ka6s/rp_adapter/BlockDiag.jpg

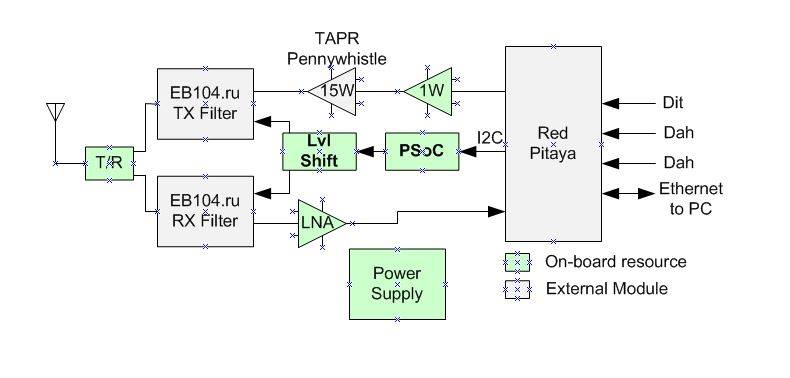
BlockDiag.jpg
