ka6s/rp_adapter/knobs_back.jpg

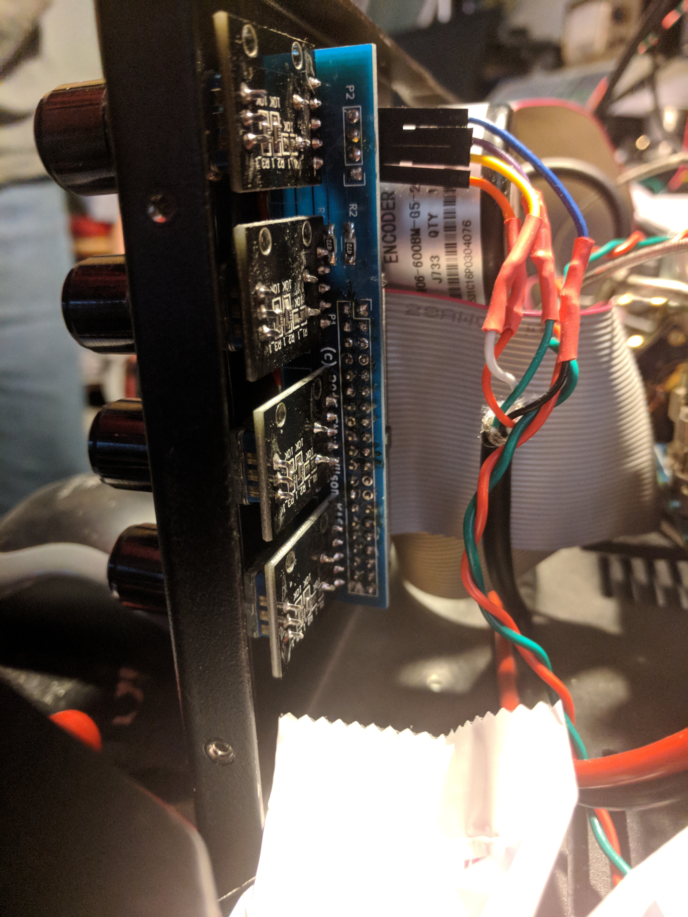
knobs_back.jpg
