ka6s/rp_adapter/messysystem.jpg

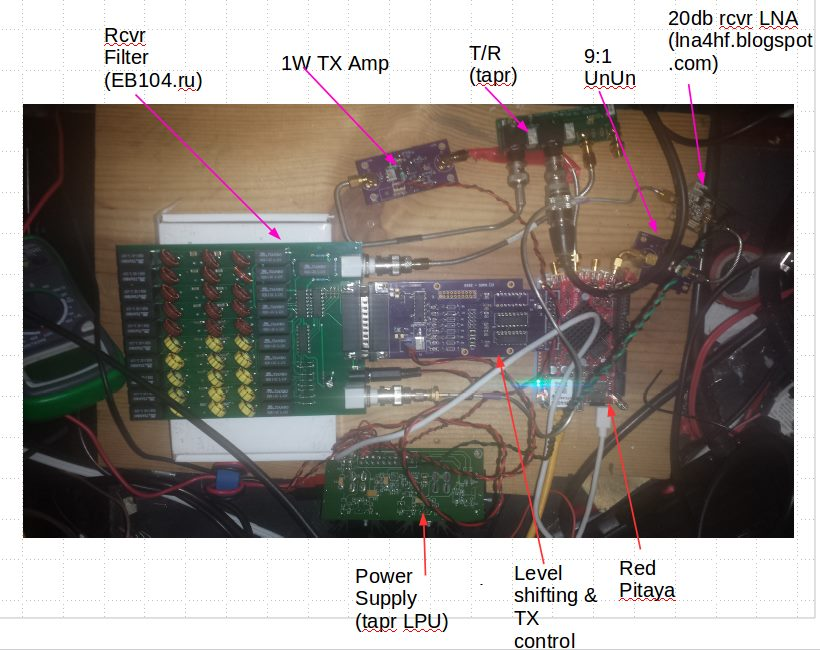
messysystem.jpg
