ka6s/rp_adapter/MezaninePower.jpeg

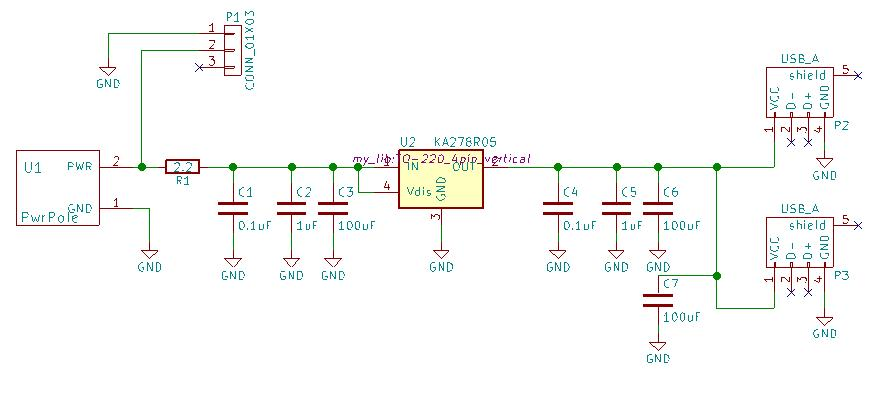
MezaninePower.jpeg
