ka6s/rp_adapter/OneWattPa.jpeg

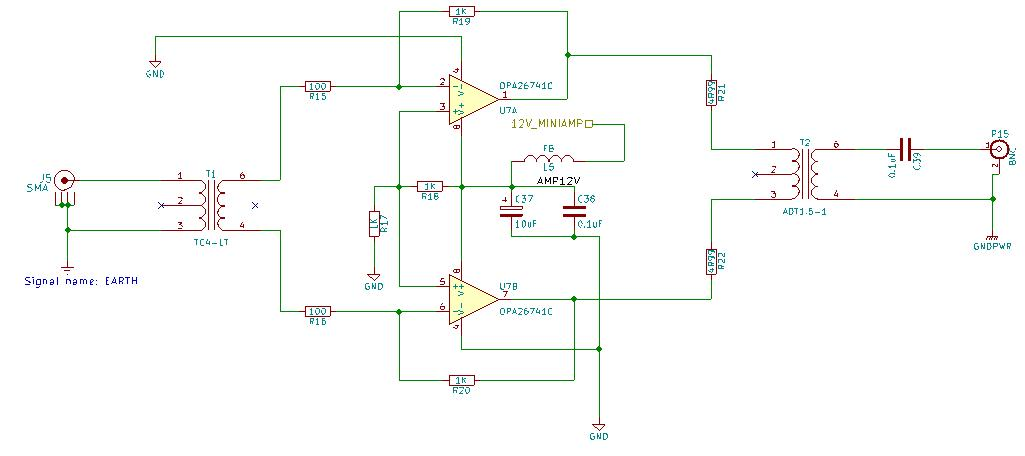
OneWattPa.jpeg
