ka6s/rp_adapter/PA.jpg

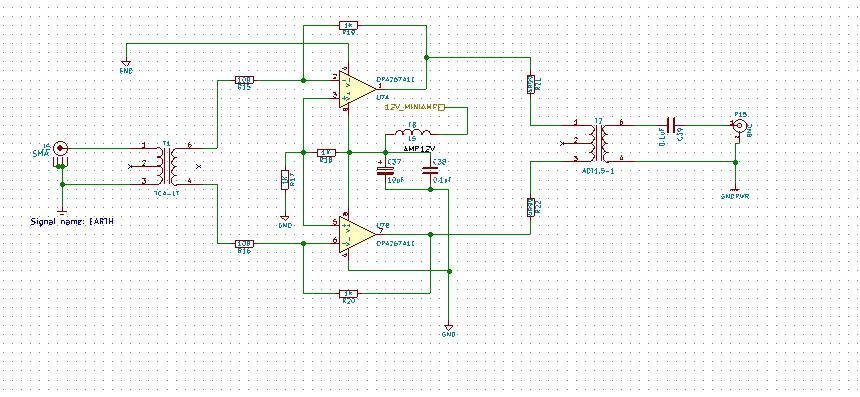
PA.jpg
