ka6s/rp_adapter/PiHPSDR_image2.jpg

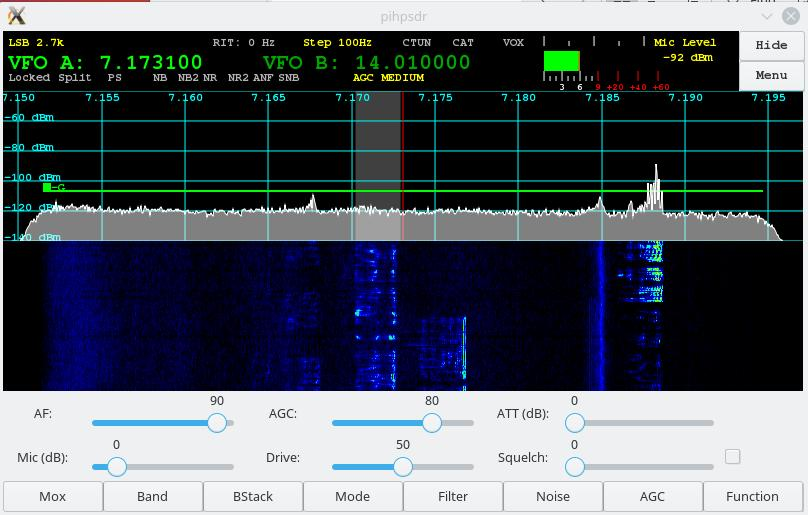
PiHPSDR_image2.jpg
