ka6s/rp_adapter/PiHPSDR_image.jpeg

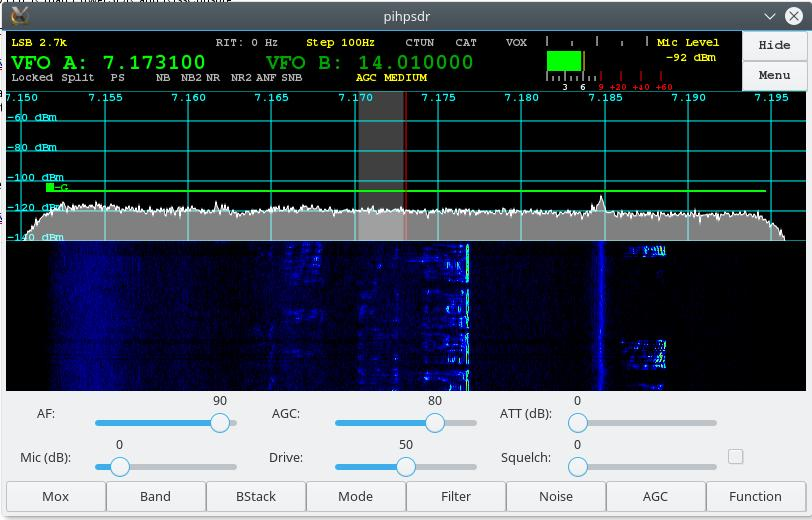
PiHPSDR_image.jpeg
