ka6s/rp_adapter/PiHPSSDR_image3.jpeg

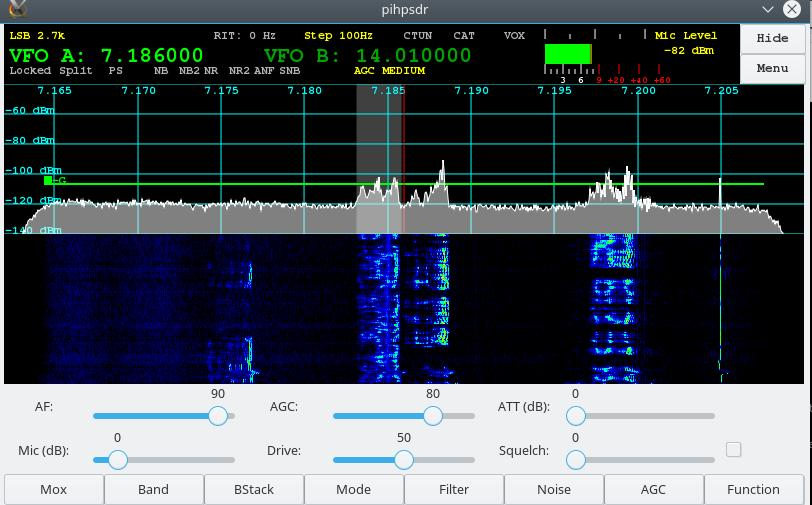
PiHPSSDR_image3.jpeg
