ka6s/rp_adapter/Power_AddOn.jpg

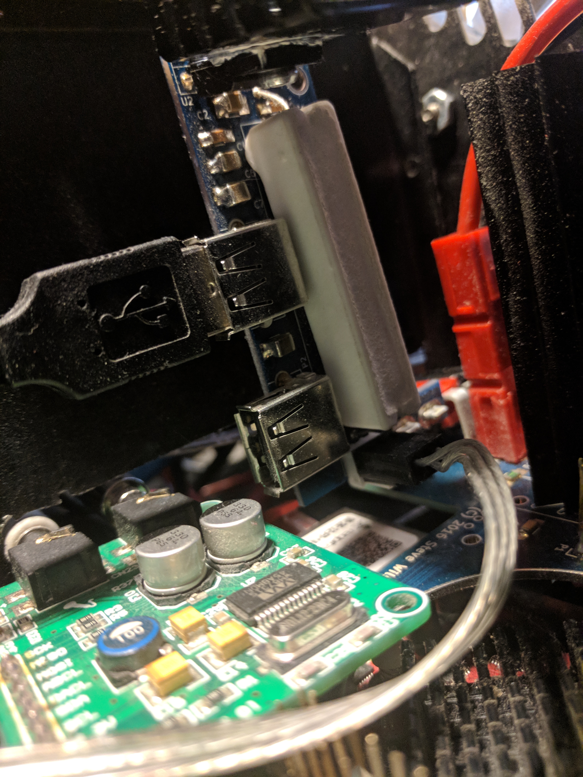
Power_AddOn.jpg
