ka6s/rp_adapter/redp.jpg

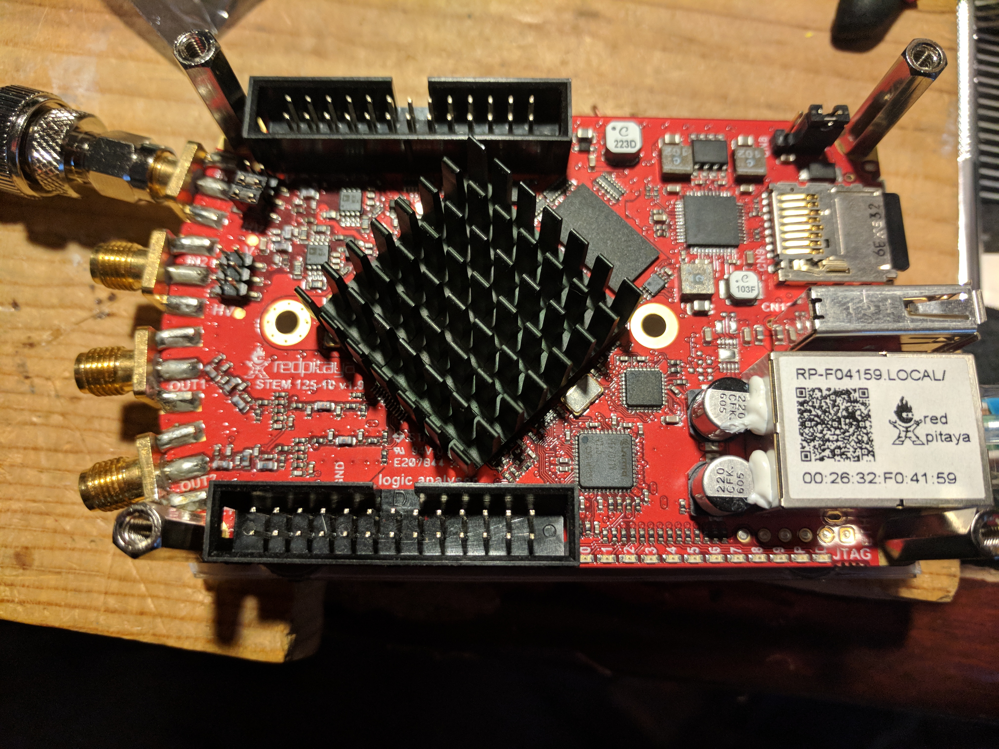
redp.jpg
