ka6s/rp_adapter/rev2.jpg

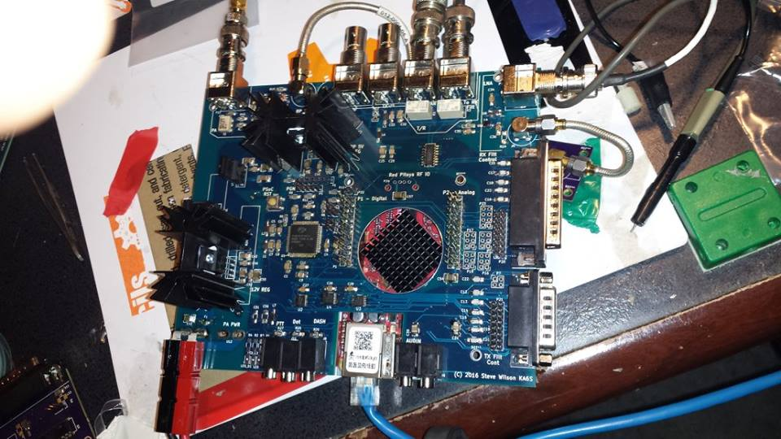
rev2.jpg
