ka6s/rp_adapter/Rev3.jpg

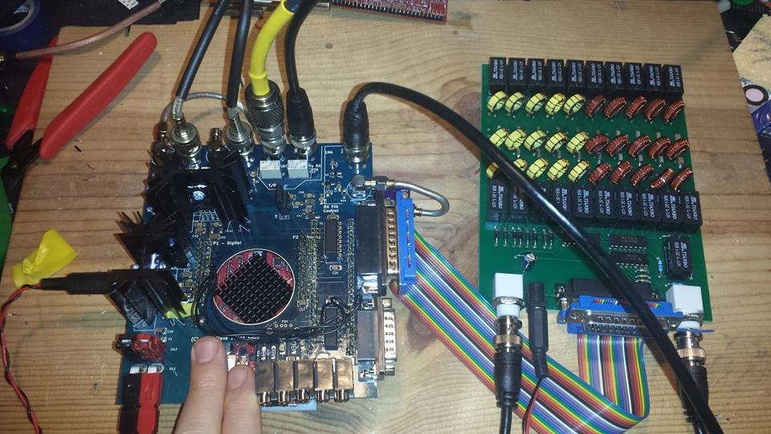
Rev3.jpg
