ka6s/rp_adapter/rev3_with_raspberrypi.jpg

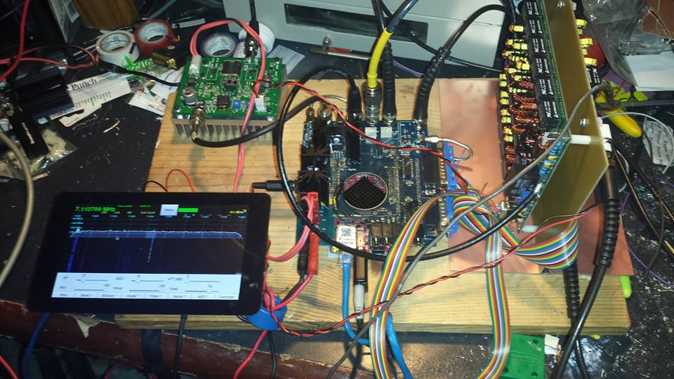
rev3_with_raspberrypi.jpg
