ka6s/rp_adapter/rotary_encoder_schem.jpeg

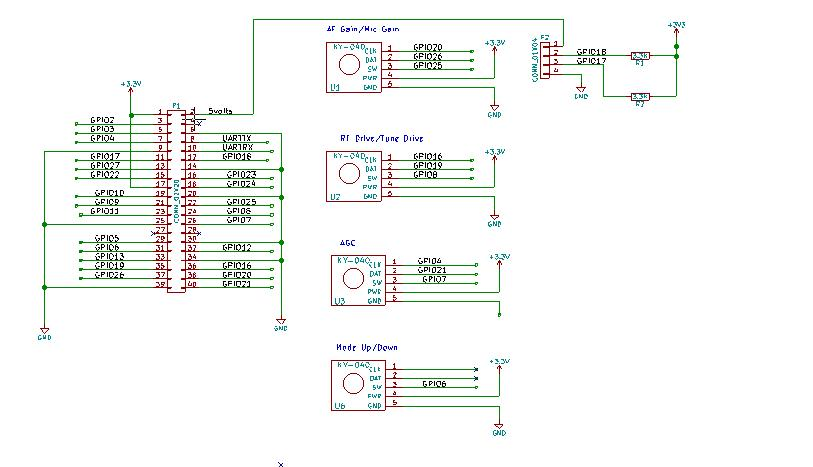
rotary_encoder_schem.jpeg
