ka6s/rp_adapter/rp2rev1.jpg

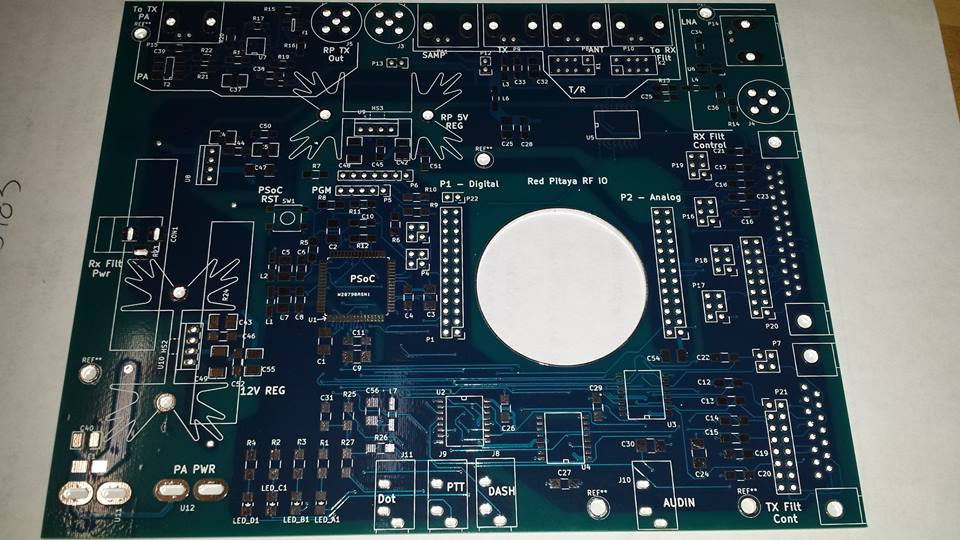
rp2rev1.jpg
