ka6s/rp_adapter/rp3_ver3_versus_ver2.jpg

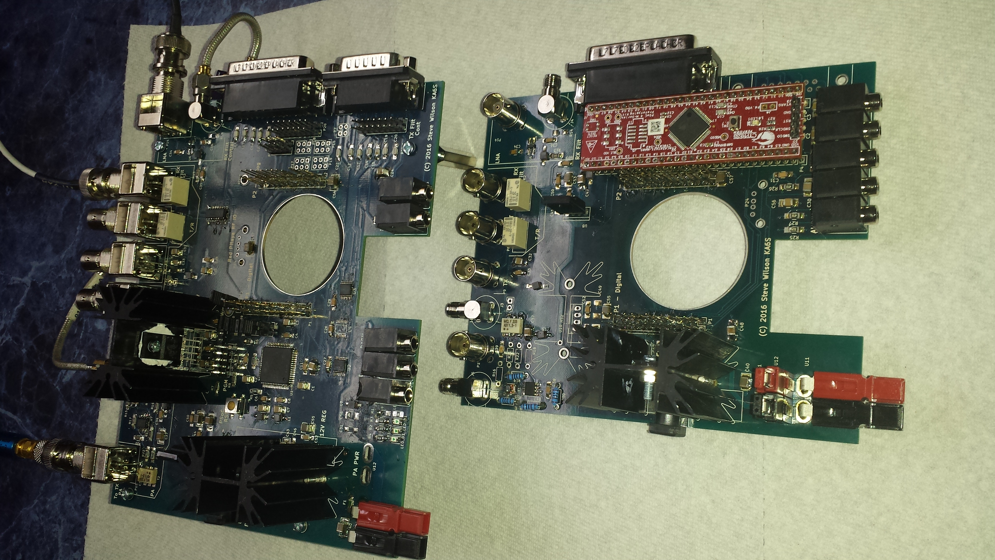
rp3_ver3_versus_ver2.jpg
