ka6s/rp_adapter/unun.jpg

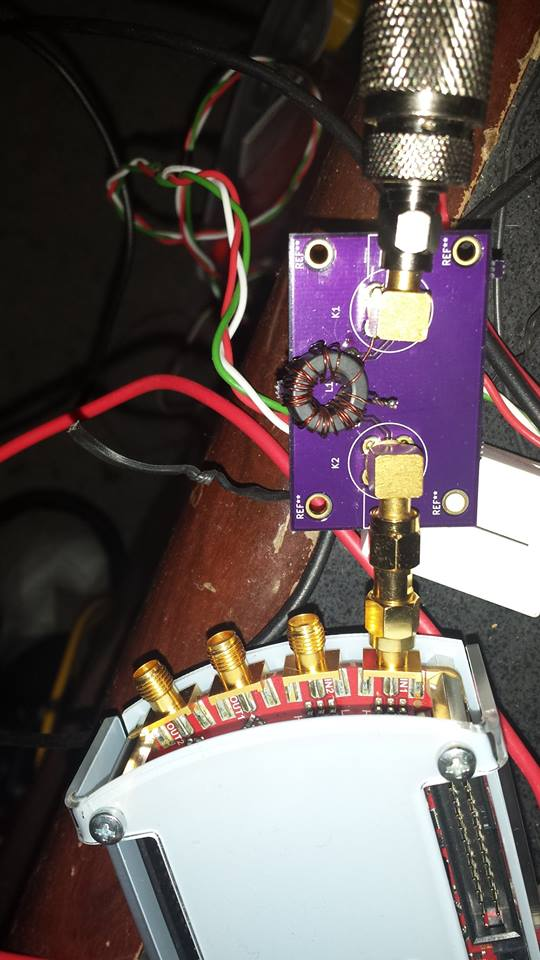
unun.jpg
