ka6s/rp_adapter/docs/rp_adapter.pdf

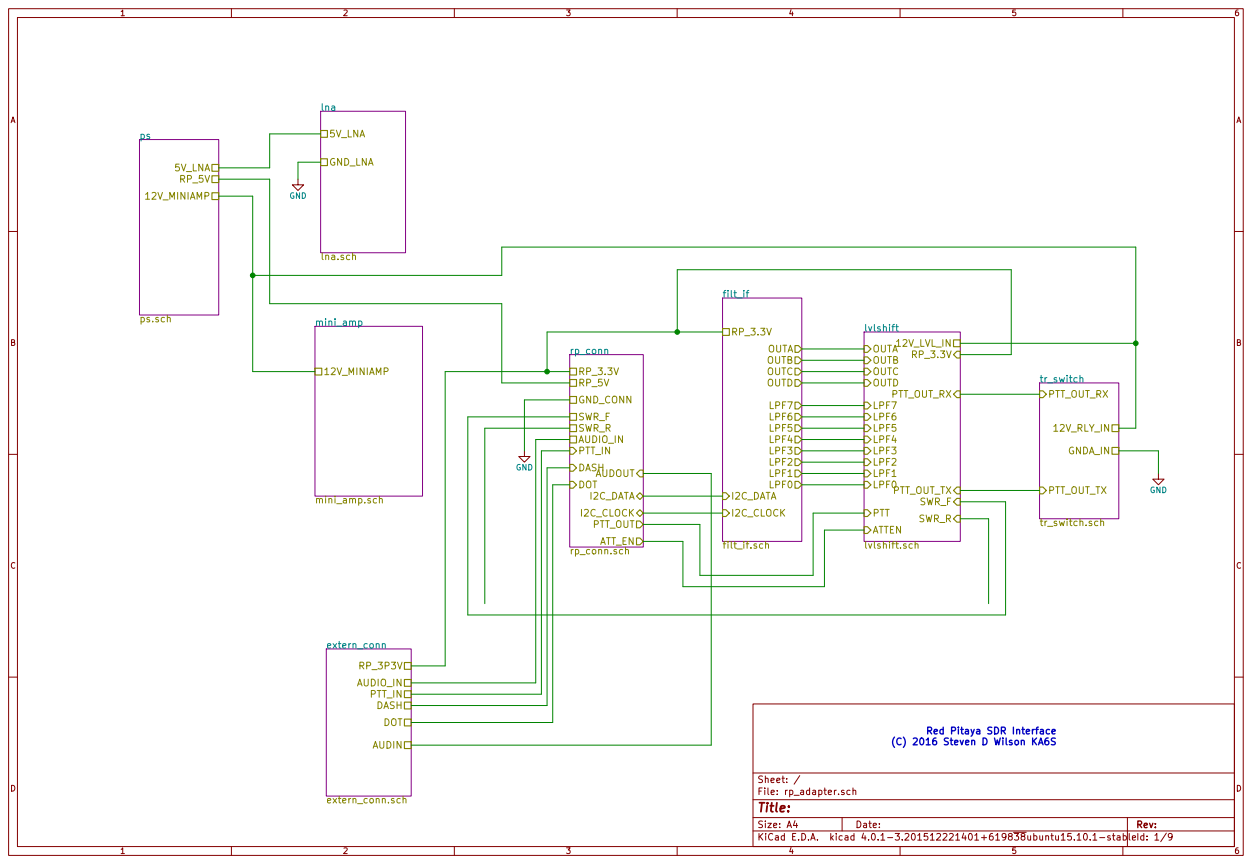
[picture p25: page 1]

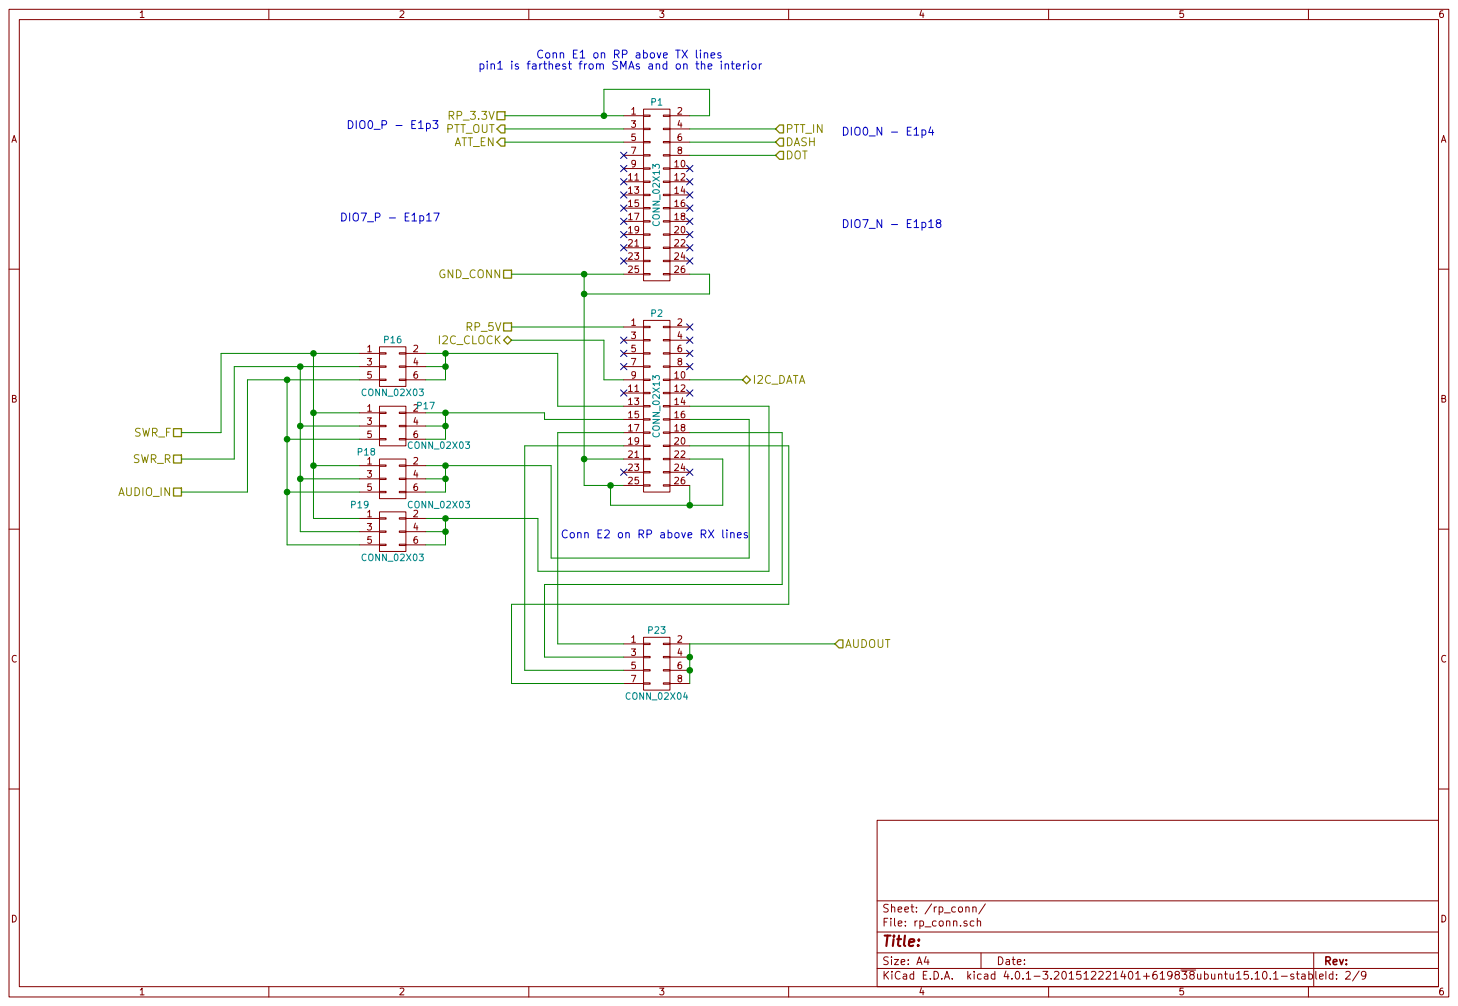
[picture p26: page 2]

pin1 is farthest from SMAs and on the interior

5 3 | 6P17 CONN_02X03 4

15 | 16
17 | 18

Conn E2 on RP above RX lines

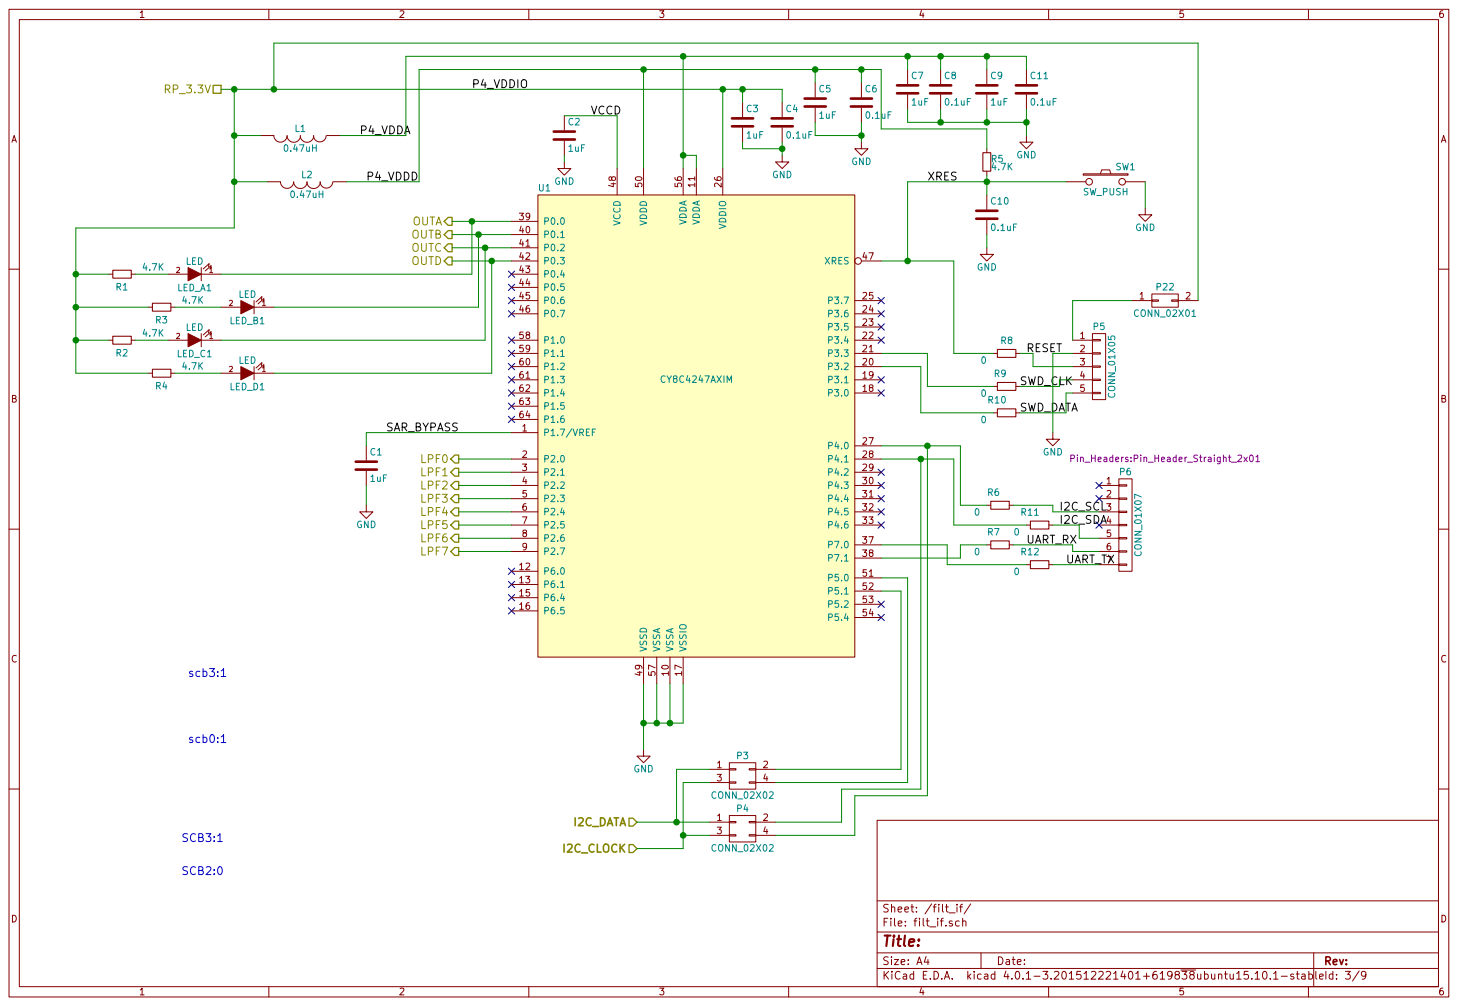
[picture p27: page 3]

VCCD | C3

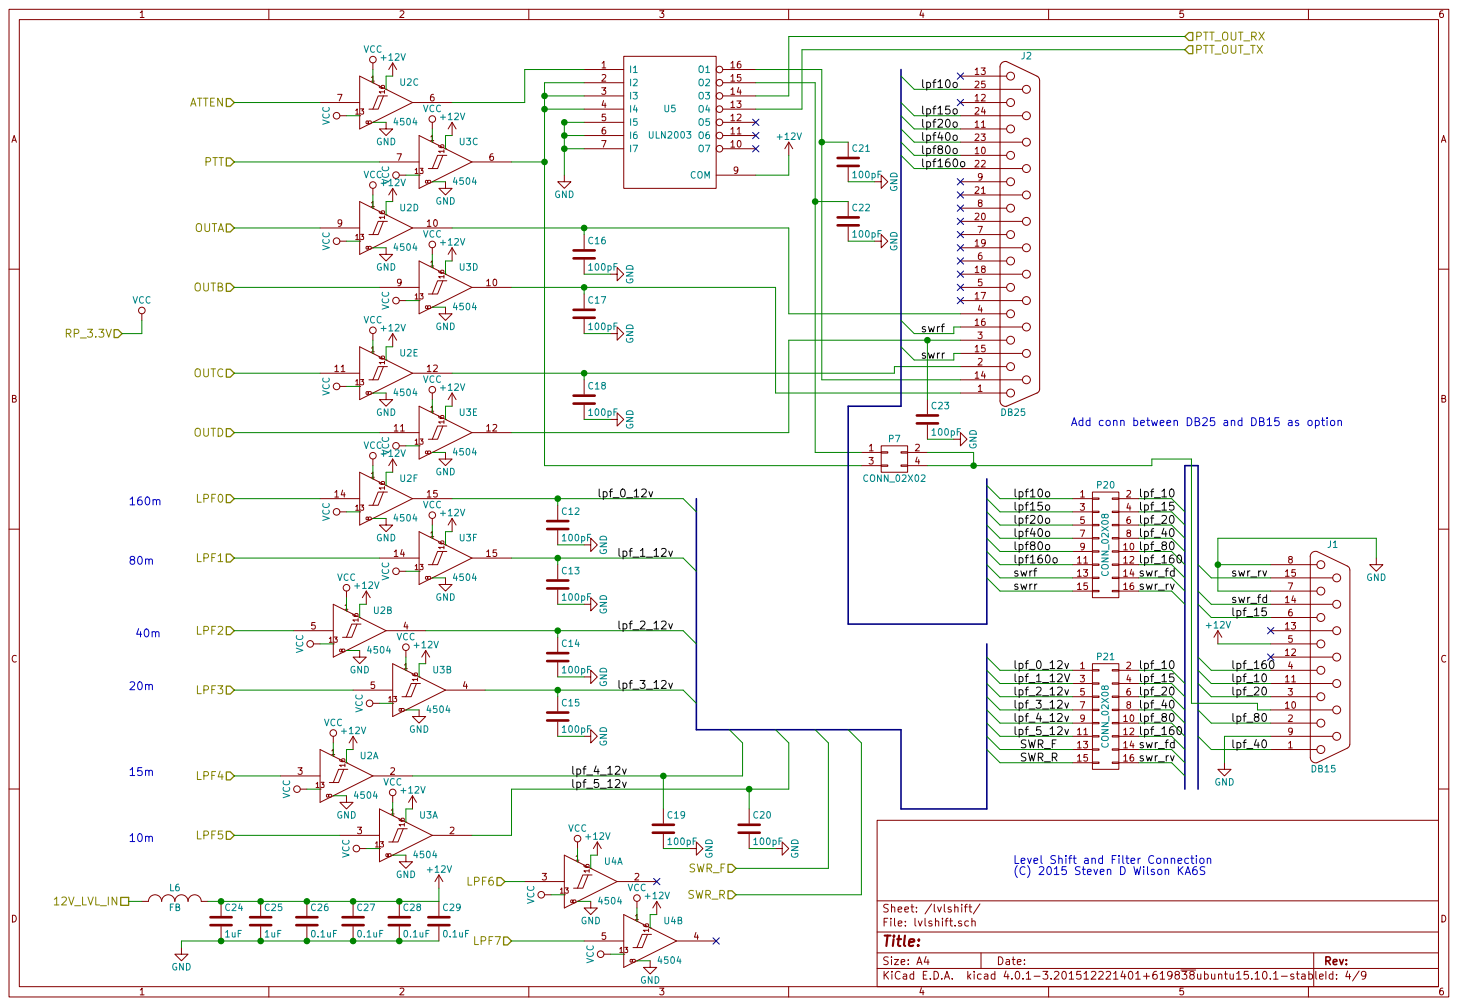
[picture p28: page 4]

14

Add conn between DB25 and DB15 as option

Level Shift and Filter Connection
(C) 2015 Steven D Wilson KA6S

Id: 4/9 Title: File: lvlshift.sch Sheet: /lvlshift/

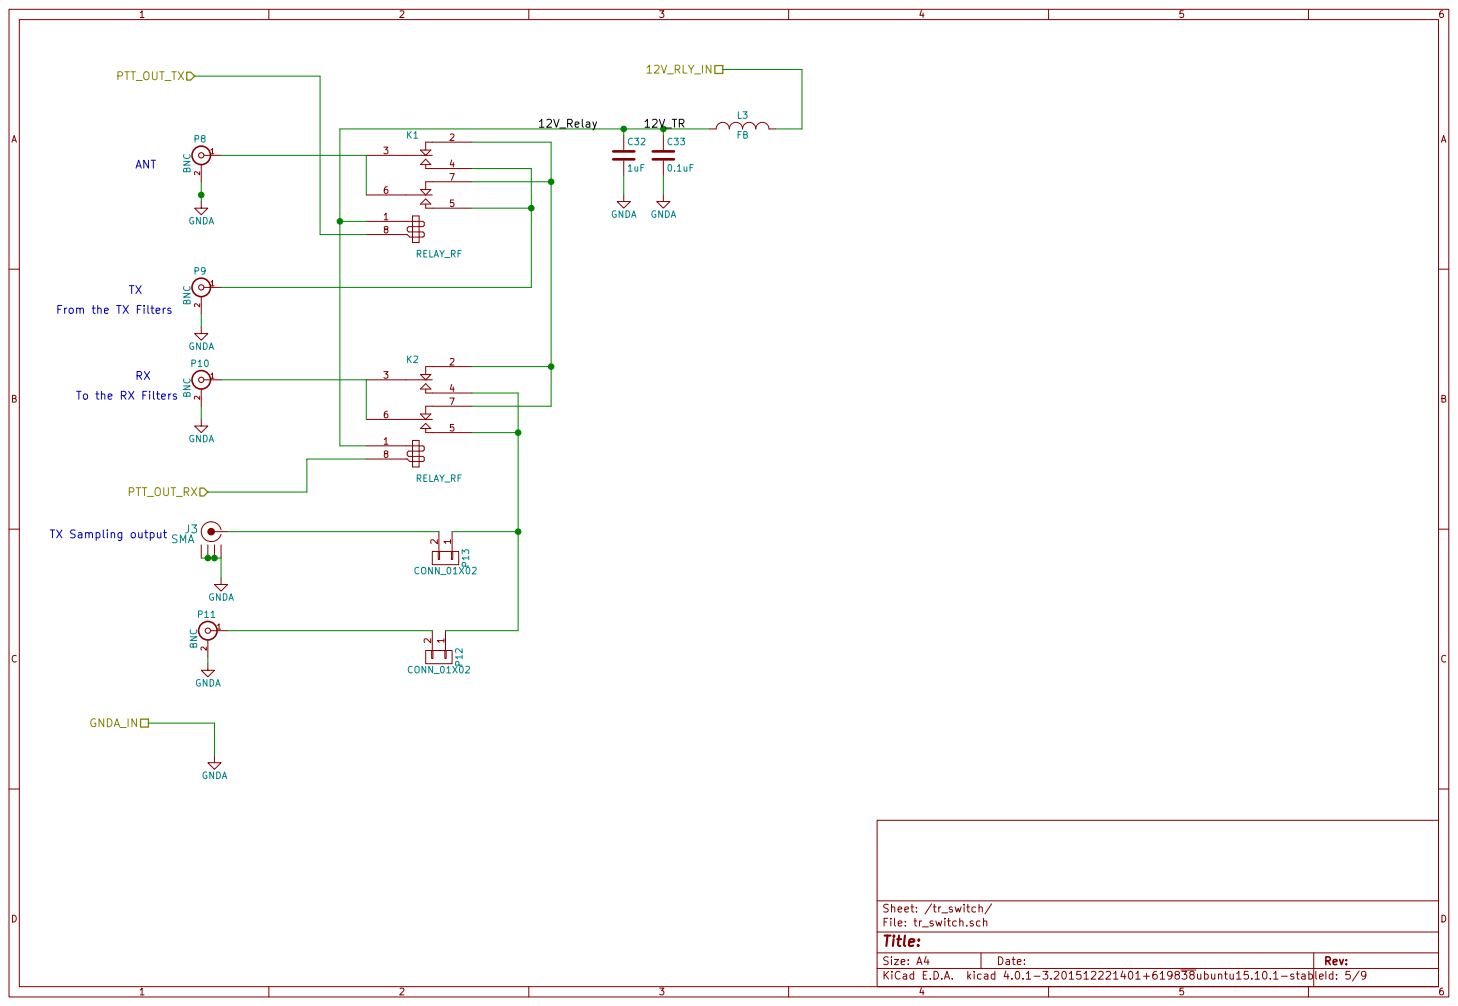
[picture p29: page 5]

2 P10 BNC GNDA To the RX Filters From the TX Filters

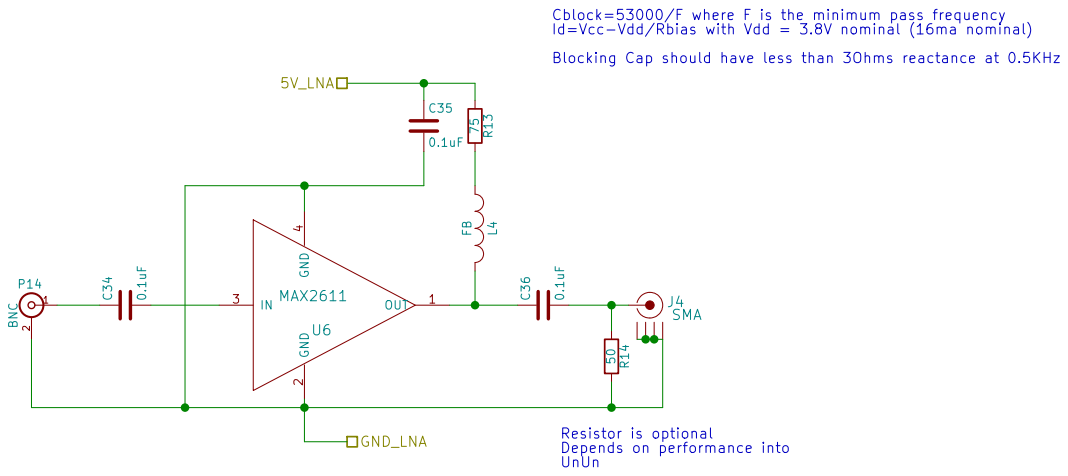
[picture p30: page 6]

Cblock=53000/F where F is the minimum pass frequency
Id=Vcc-Vdd/Rbias with Vdd = 3.8V nominal (16ma nominal)
Blocking Cap should have less than 3Ohms reactance at 0.5KHz

Depends on performance into UnUn GND_LNA

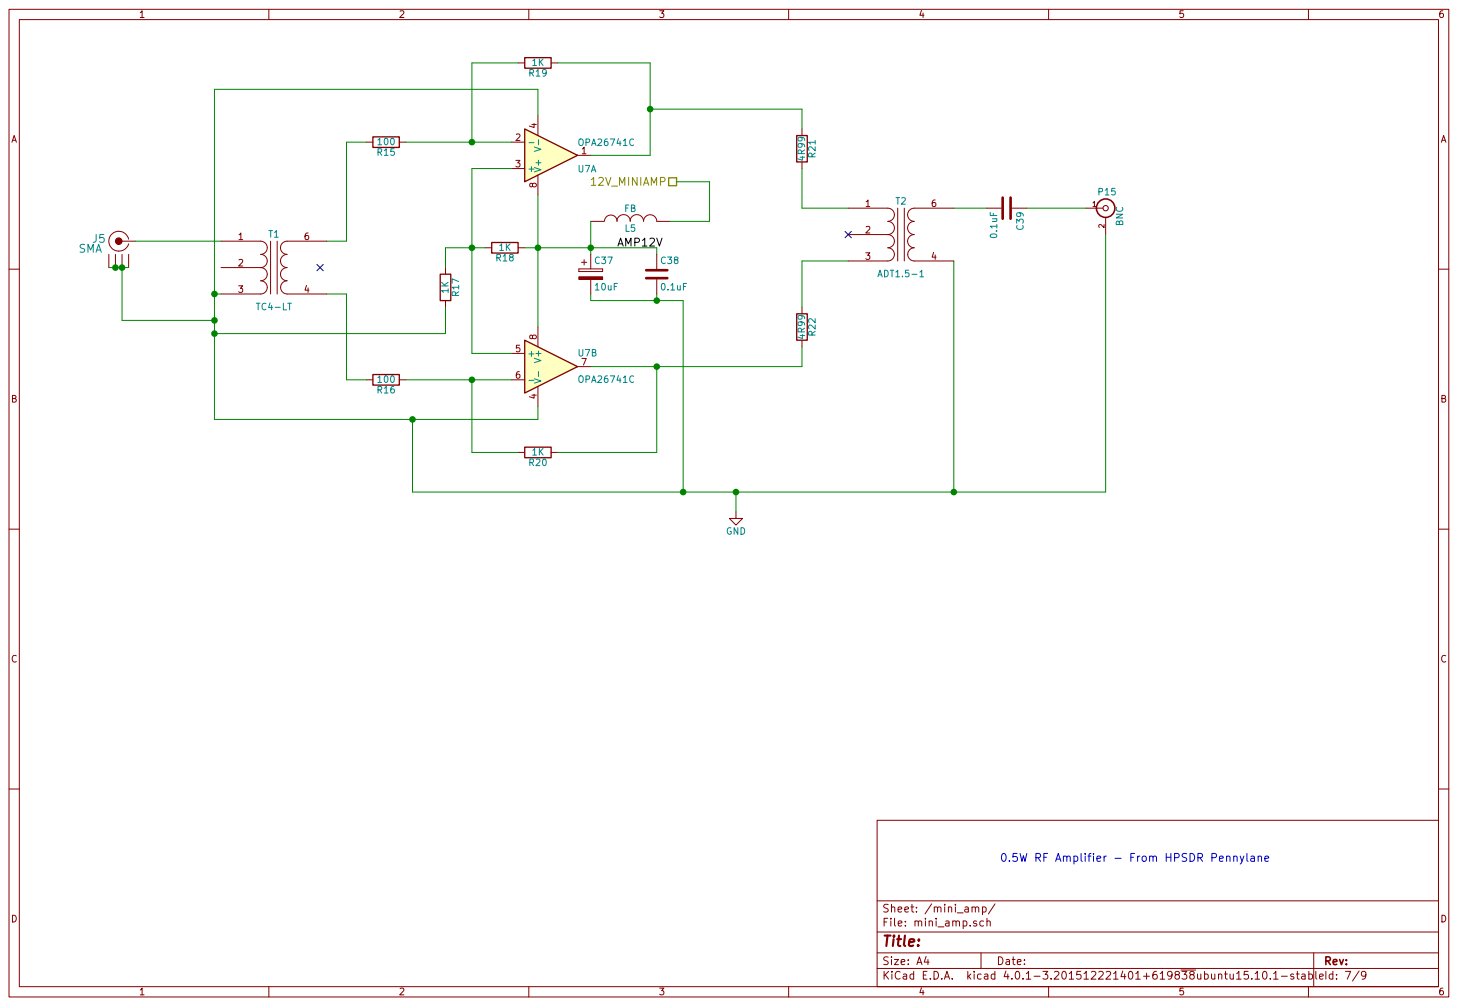
[picture p31: page 7]

0.5W RF Amplifier - From HPSDR Pennylane

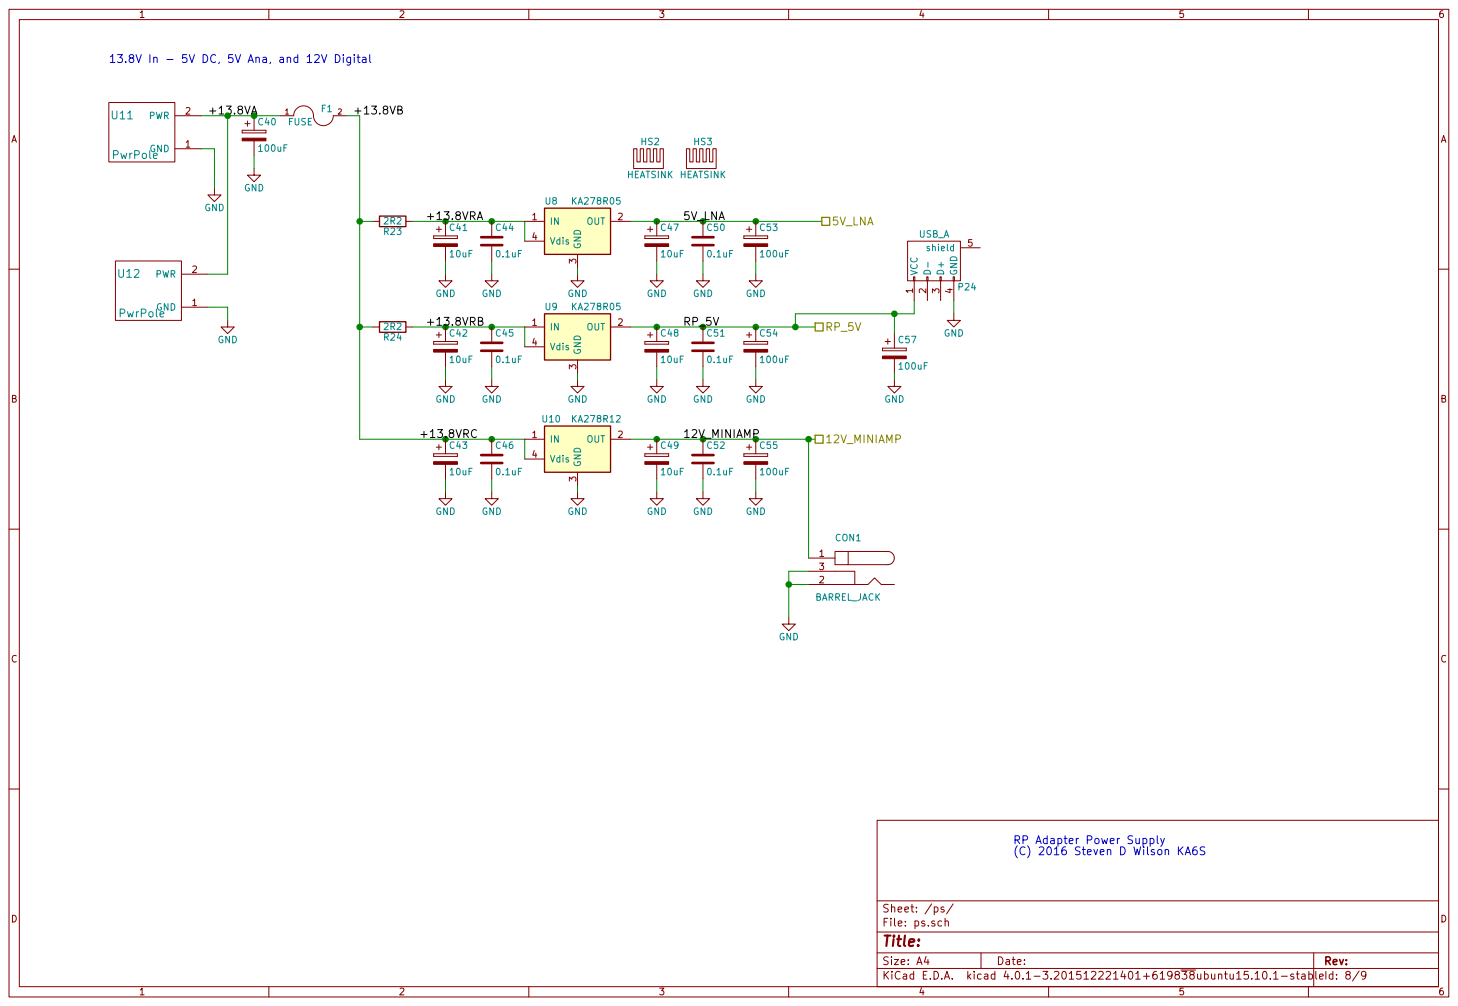
[picture p32: page 8]

13.8V In - 5V DC, 5V Ana, and 12V Digital

3 Vdis 4 U8 KA278R05 GND GND GND GND GND GND GND GND

RP Adapter Power Supply
(C) 2016 Steven D Wilson KA6S

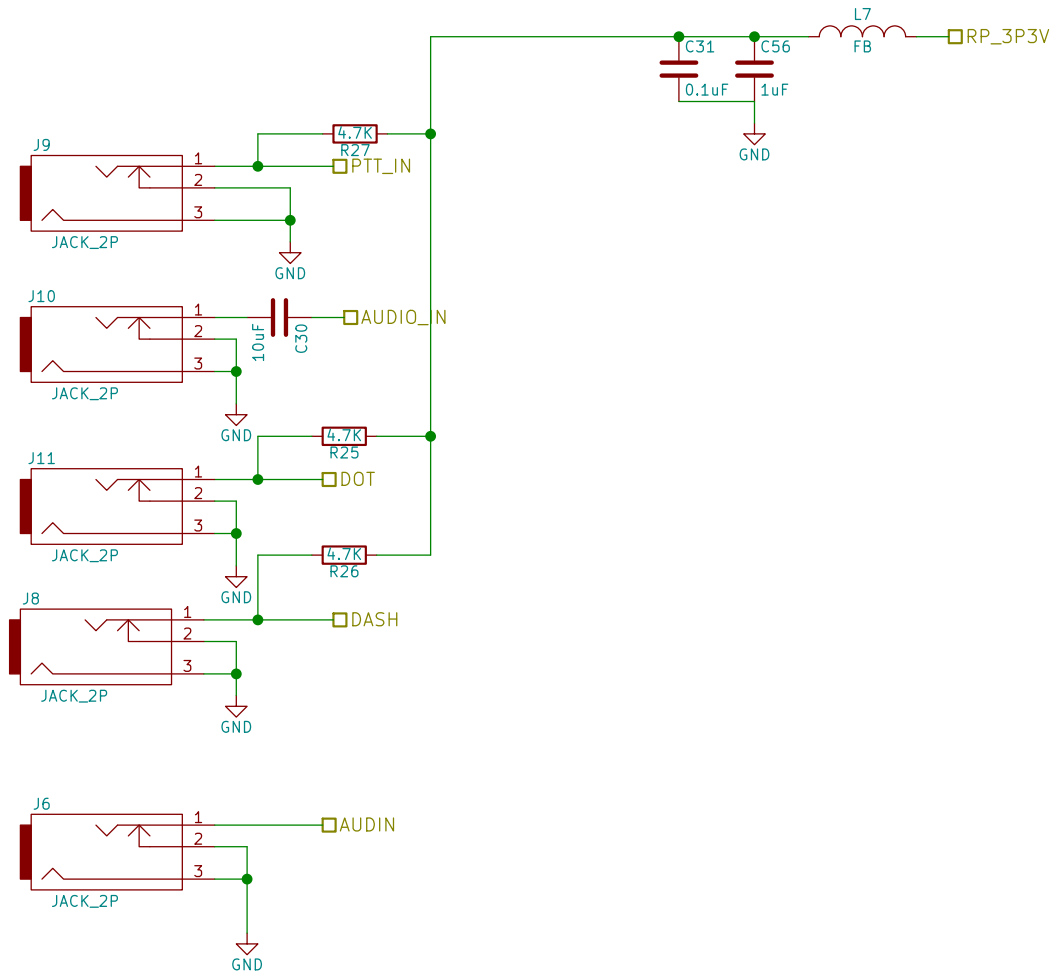
[picture p33: page 9]
