ka6s/rp_adapter/docs/rp_conn-rp_conn.pdf

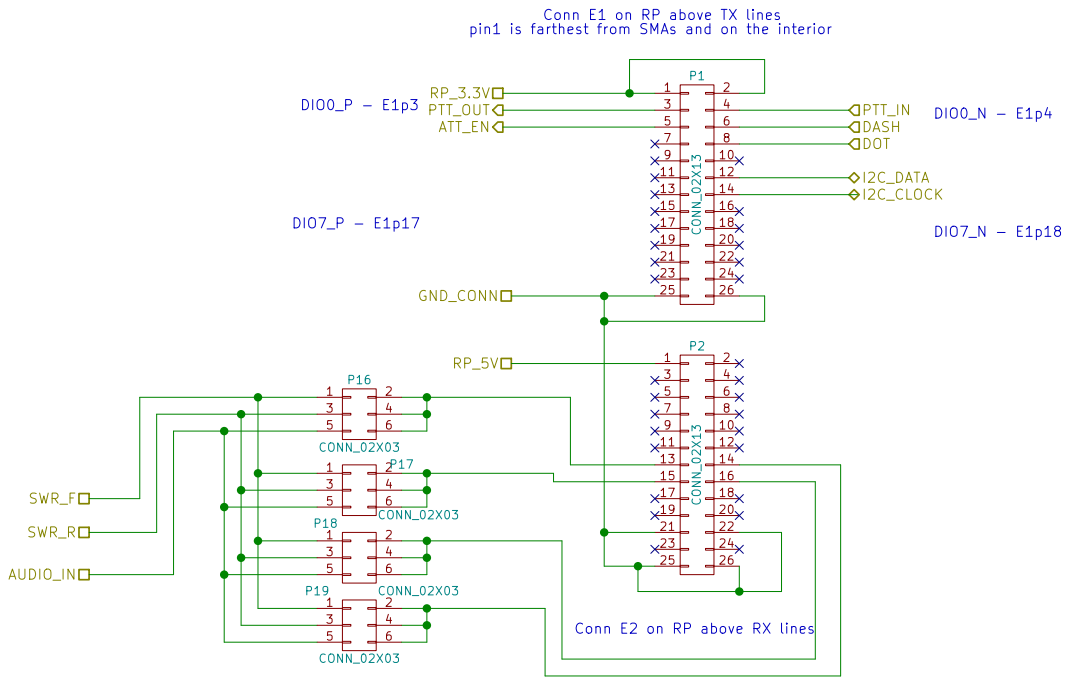
[picture p41: page 1]

pin1 is farthest from SMAs and on the interior

19 P2CONN_02X13 11 13

5 3 | | 6P17 CONN_02X03 4

15 | | 16
17 21 | | 18

Conn E2 on RP above RX lines
